Dennis-van-Gils/project-Humidistat/docs/photos/soldering_3.jpg

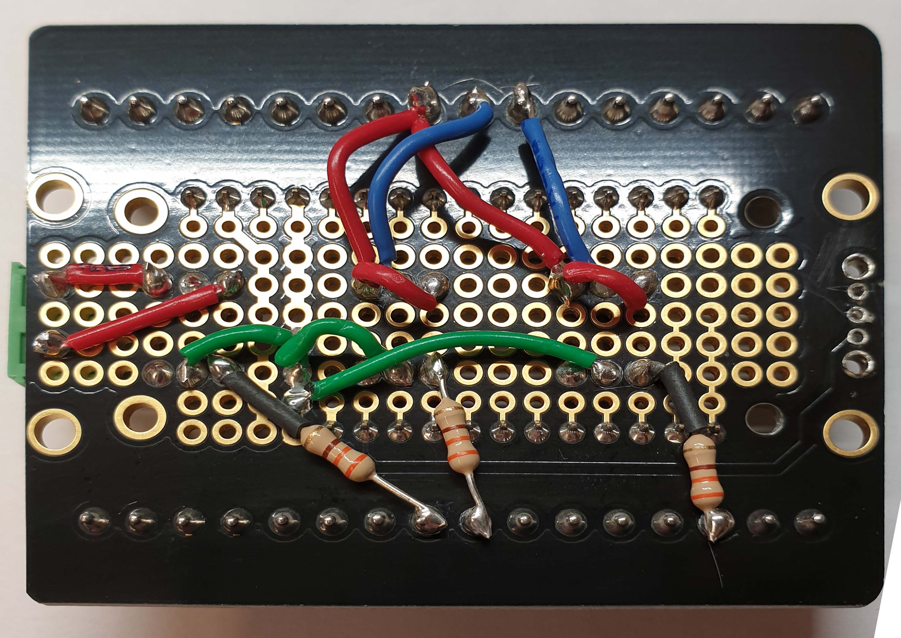
docs/photos/soldering_3.jpg
